purduerov/X17-Backplane/BackplaneSymbol+Footprint/430450612/430450612.stp

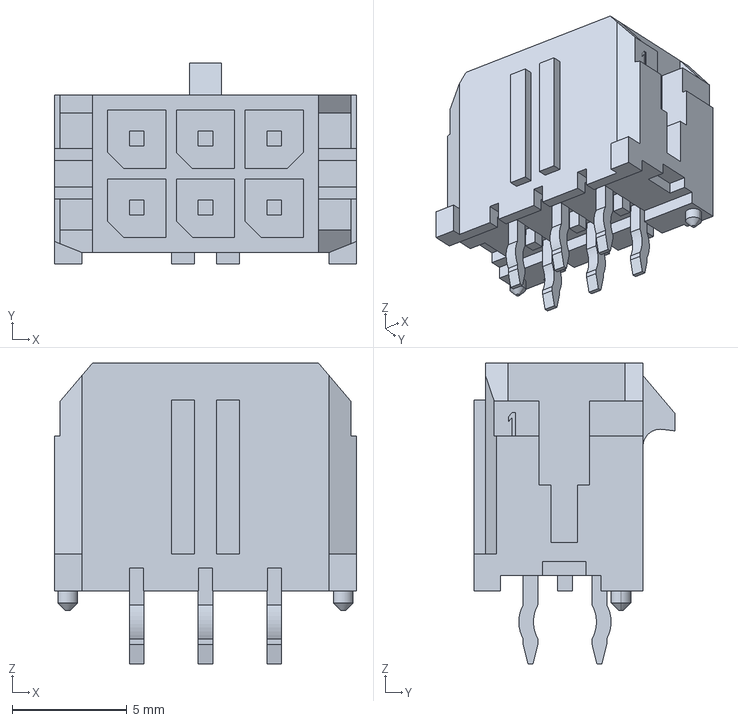
[picture p15: CAD file, 2025-01-12]
BackplaneSymbol+Footprint/430450612/430450612.stp
13.2 x 8.77 x 13.1 mm
